khinds10/MagicMirror/images/MagicMirror2.jpg

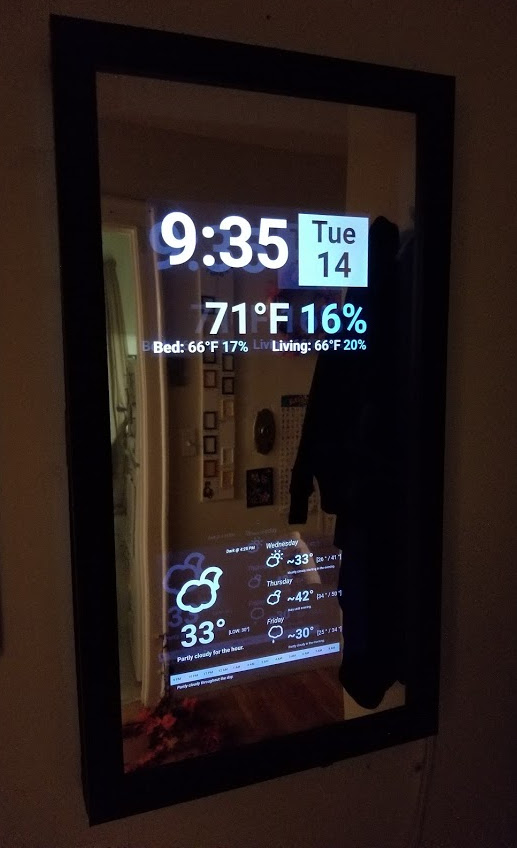
images/MagicMirror2.jpg
