khinds10/MagicMirror/tablet/img/tile-wide.png

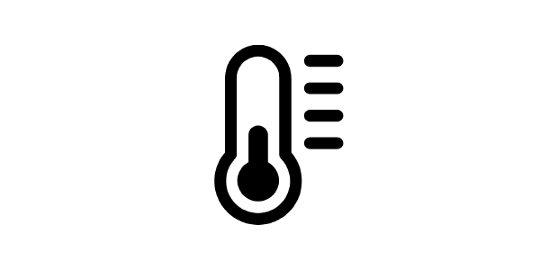
tablet/img/tile-wide.png
